zenitheesc/Probe-CDH/KiCad_Files/shapes3D/2AD6-1262 G-NiceRF.step

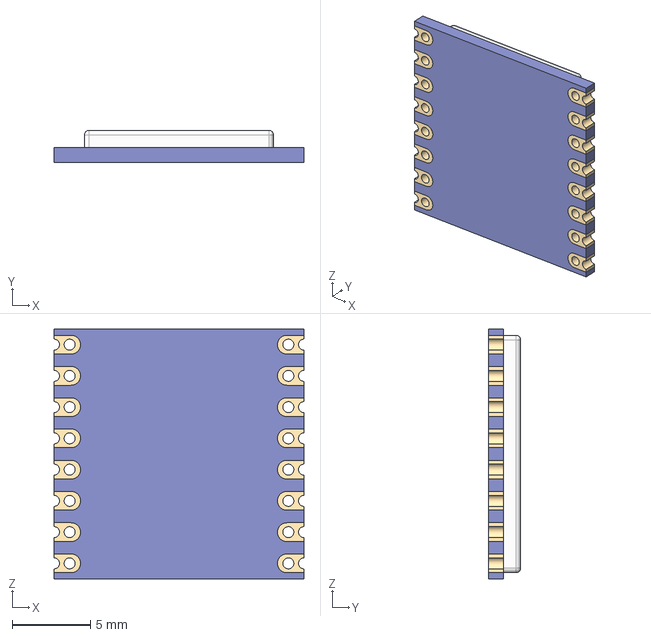
[picture p23: CAD file, 2022-01-20]
KiCad_Files/shapes3D/2AD6-1262 G-NiceRF.step
16.0 x 2.08 x 16.0 mm
