zenitheesc/Probe-CDH/KiCad_Files/shapes3D/SO-8_5.3x6.2mm_P1.27mm.step

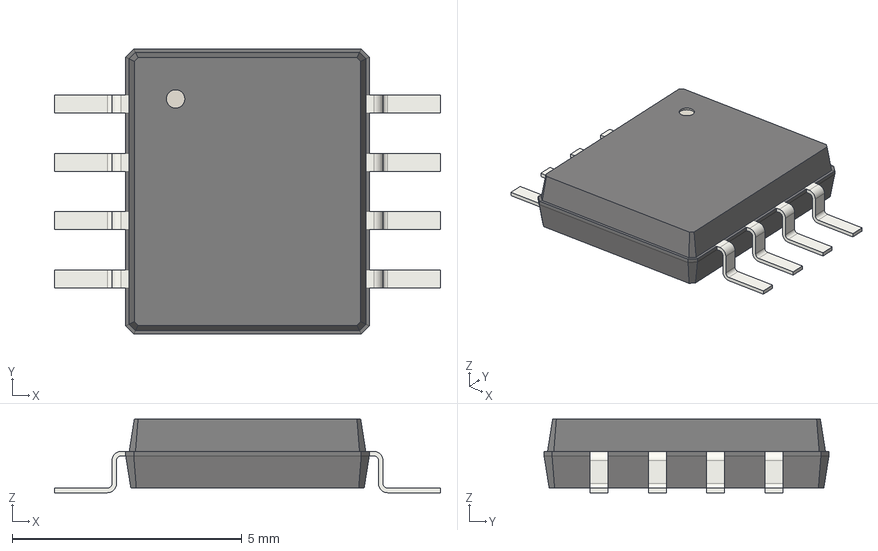
[picture p24: CAD file, 2022-01-20]
KiCad_Files/shapes3D/SO-8_5.3x6.2mm_P1.27mm.step
8.40 x 6.20 x 1.60 mm
