zenitheesc/Probe-CDH/KiCad_Files/shapes3D/LoRa126XF30.step

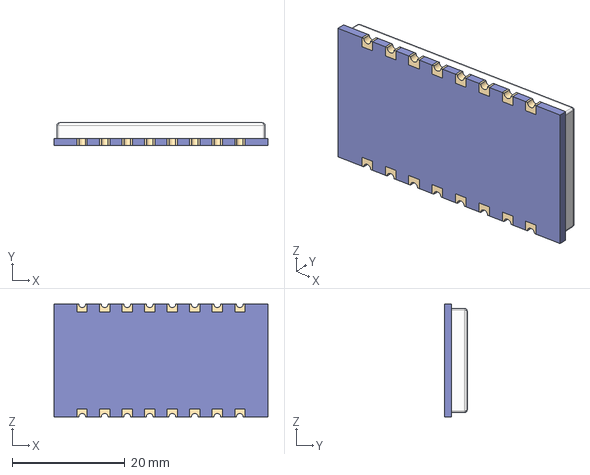
[picture p25: CAD file, 2022-01-20]
KiCad_Files/shapes3D/LoRa126XF30.step
38.0 x 4.00 x 20.0 mm
