zenitheesc/Probe-CDH/KiCad_Files/shapes3D/Molex - 73391-0060.step

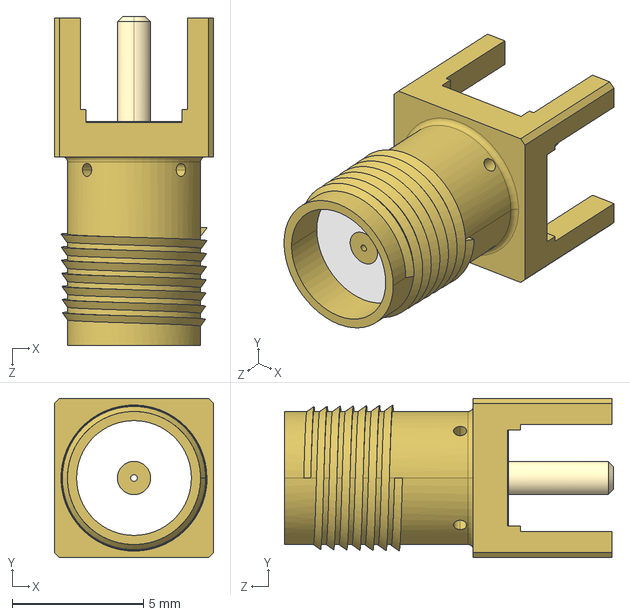
[picture p26: CAD file, 2022-01-20]
KiCad_Files/shapes3D/Molex - 73391-0060.step
6.08 x 6.08 x 12.6 mm
