zenitheesc/Probe-CDH/KiCad_Files/shapes3D/D_0603_1608Metric.step

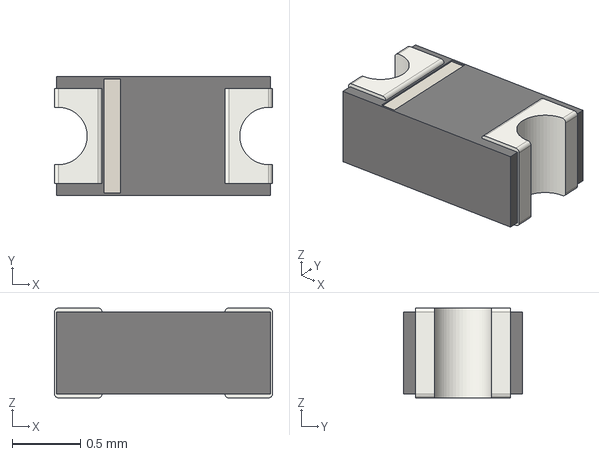
[picture p27: CAD file, 2022-01-20]
KiCad_Files/shapes3D/D_0603_1608Metric.step
1.60 x 0.87 x 0.66 mm
