zenitheesc/Probe-CDH/KiCad_Files/shapes3D/R_0603_1608Metric.step

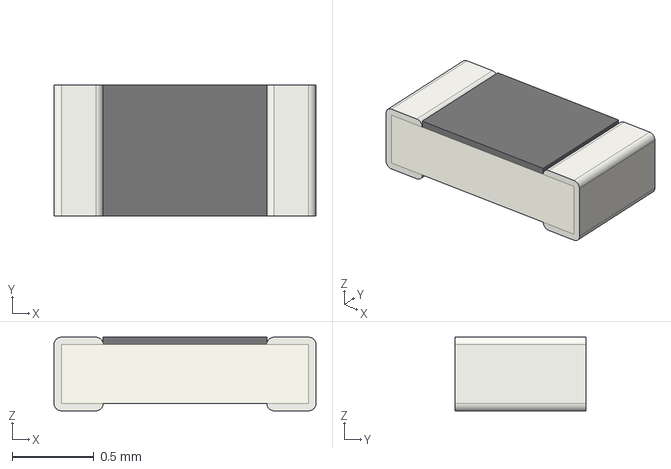
[picture p28: CAD file, 2022-01-20]
KiCad_Files/shapes3D/R_0603_1608Metric.step
1.60 x 0.8 x 0.45 mm
