zenitheesc/Probe-CDH/KiCad_Files/shapes3D/Crystal_SMD_MicroCrystal_CC7V-T1A-2Pin_3.2x1.5mm.step

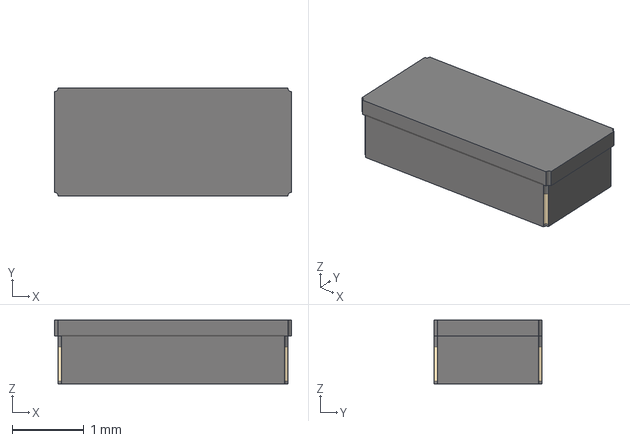
[picture p29: CAD file, 2022-01-20]
KiCad_Files/shapes3D/Crystal_SMD_MicroCrystal_CC7V-T1A-2Pin_3.2x1.5mm.step
3.30 x 1.50 x 0.89 mm
