zenitheesc/Probe-CDH/KiCad_Files/shapes3D/SOT-23.step

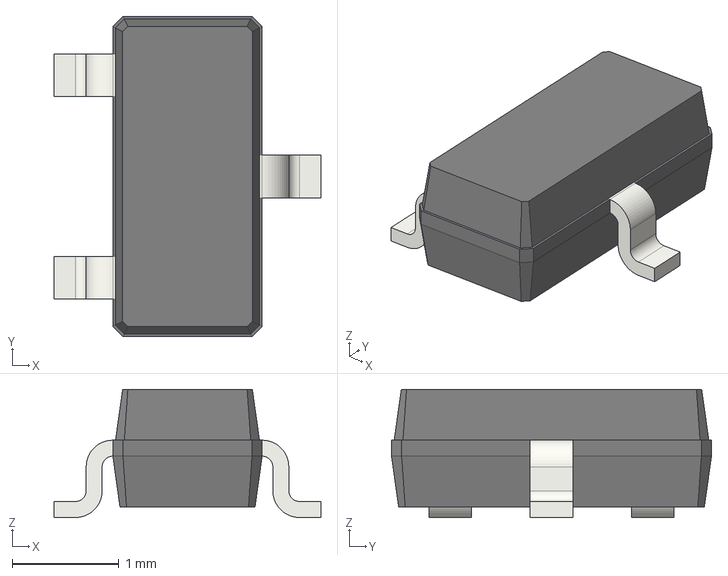
[picture p31: CAD file, 2022-01-20]
KiCad_Files/shapes3D/SOT-23.step
2.50 x 3.00 x 1.20 mm
