zenitheesc/Probe-CDH/KiCad_Files/shapes3D/C_0805_2012Metric.step

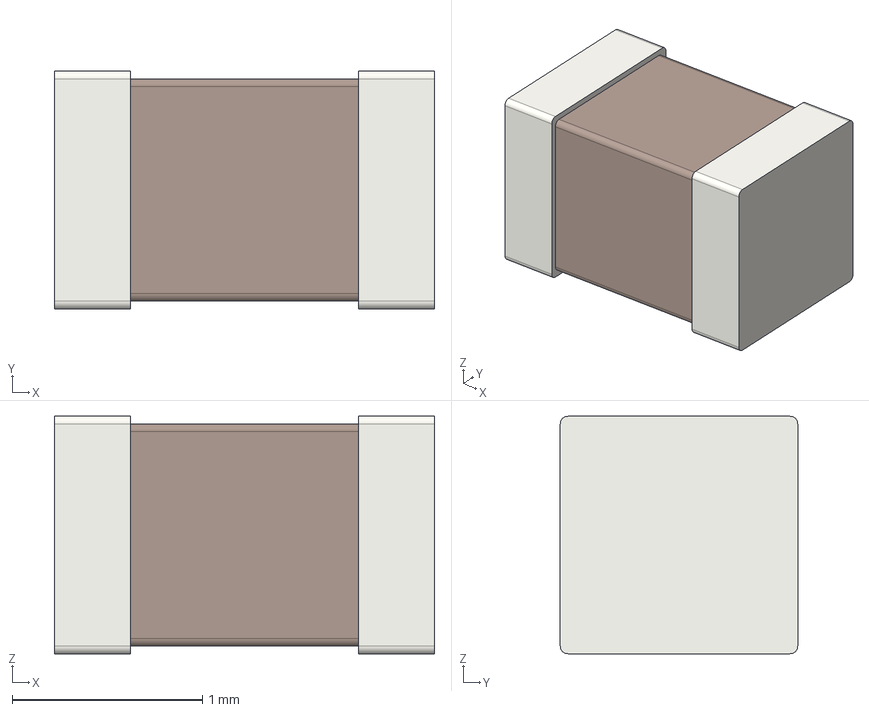
[picture p32: CAD file, 2022-01-20]
KiCad_Files/shapes3D/C_0805_2012Metric.step
2.00 x 1.25 x 1.25 mm
