zenitheesc/Probe-CDH/KiCad_Files/shapes3D/MEM2075-00-140-01-A.stp

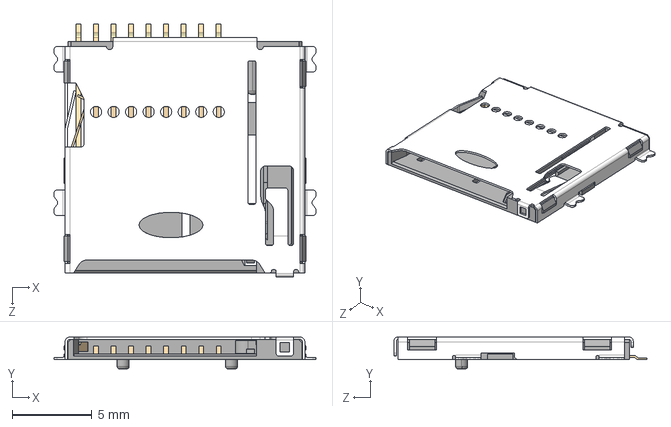
[picture p33: CAD file, 2022-01-20]
KiCad_Files/shapes3D/MEM2075-00-140-01-A.stp
16.4 x 2.00 x 15.9 mm
