zenitheesc/Probe-CDH/KiCad_Files/shapes3D/D2PAK-2 L7805.step

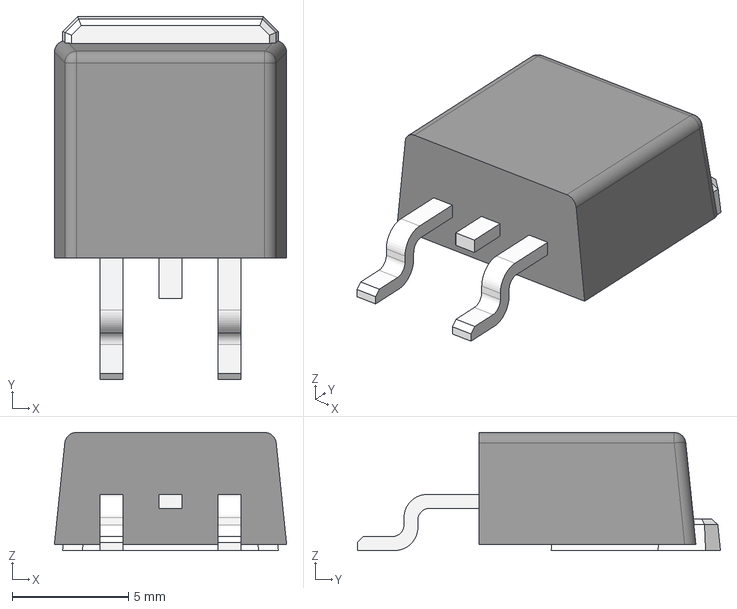
[picture p35: CAD file, 2022-01-20]
KiCad_Files/shapes3D/D2PAK-2 L7805.step
10.0 x 15.6 x 5.08 mm
