zenitheesc/Probe-CDH/KiCad_Files/shapes3D/L_0402_1005Metric.step

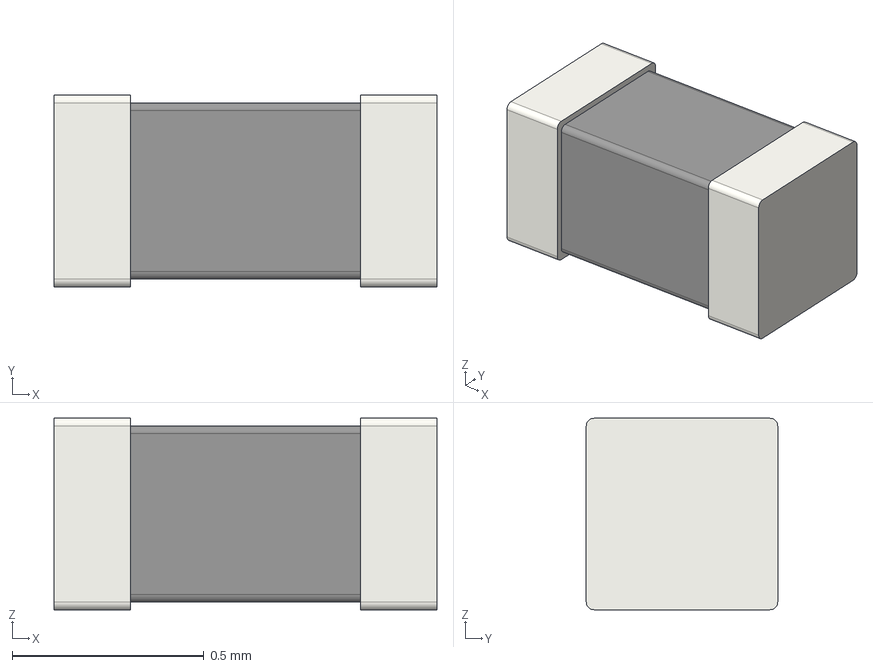
[picture p37: CAD file, 2022-01-20]
KiCad_Files/shapes3D/L_0402_1005Metric.step
1.00 x 0.5 x 0.5 mm
